rasteri/TAStm32/Src/usbplayback/gfx.c

#include <stdint.h>

const uint8_t GFX_CENTER[] = {
	0x00,0x00,
	0x00,0x00,
	0x00,0x00,
	0xc0,0x01,
	0x30,0x06,
	0x08,0x08,
	0x04,0x10,
	0x02,0x20,
	0x02,0x20,
	0x01,0x40,
	0x01,0x40,
	0x01,0x40,
	0x02,0x20,
	0x02,0x20,
	0x04,0x10,
	0x08,0x08,
	0x30,0x06,
	0xc0,0x01,
	0x00,0x00,
	0x00,0x00,
	0x00,0x00
};

const uint8_t GFX_START_ON[] = {
	//starton
	0x00,0xf0,0x03,
	0x00,0xfc,0x0f,
	0x00,0xfe,0x1f,
	0x00,0xc7,0x3b,
	0x00,0x83,0x33,
	0x80,0x1b,0x77,
	0x80,0x3b,0x77,
	0x80,0x3b,0x76,
	0x80,0x73,0x70,
	0x80,0xf7,0x78,
	0x80,0xff,0x7f,
	0x80,0xdf,0x7f,
	0x80,0x0f,0x78,
	0x80,0x07,0x70,
	0x80,0xdf,0x77,
	0x80,0xff,0x7f,
	0x80,0xbf,0x79,
	0x80,0xdf,0x70,
	0x80,0x5f,0x76,
	0x80,0x5f,0x77,
	0x80,0x1f,0x70,
	0x80,0x3f,0x70,
	0x80,0xff,0x7f,
	0x80,0xff,0x7f,
	0x80,0x1f,0x70,
	0x80,0x1f,0x70,
	0x80,0xdf,0x7f,
	0x80,0xdf,0x7f,
	0x80,0xdf,0x7f,
	0x80,0x0f,0x78,
	0x80,0x07,0x70,
	0x00,0xdf,0x37,
	0x00,0xff,0x3f,
	0x00,0xfe,0x1f,
	0x00,0xfc,0x0f,
	0x00,0xf0,0x03
};

const uint8_t GFX_SELECT_ON[] = {
	//selecton
	0xc0,0x0f,0x00,
	0x10,0x37,0x00,
	0x08,0x66,0x00,
	0x6c,0xee,0x00,
	0x6c,0xec,0x00,
	0xee,0xec,0x01,
	0xce,0xe0,0x01,
	0xde,0xf1,0x01,
	0xfe,0xff,0x01,
	0x7e,0xf0,0x01,
	0x3e,0xe0,0x01,
	0xbe,0xed,0x01,
	0xbe,0xed,0x01,
	0x3e,0xe4,0x01,
	0x7e,0xf4,0x01,
	0x0e,0xe0,0x01,
	0x0e,0xe0,0x01,
	0xfe,0xff,0x01,
	0x7e,0xf0,0x01,
	0x3e,0xe0,0x01,
	0xbe,0xed,0x01,
	0xbe,0xed,0x01,
	0x3e,0xe4,0x01,
	0x7e,0xf4,0x01,
	0x7e,0xf0,0x01,
	0x3e,0xe0,0x01,
	0xbe,0xef,0x01,
	0xbe,0xef,0x01,
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
		0xff,0x07,0x00,0x00,
		0xff,0x03,0x00,0x00,
		0xff,0x01,0x00,0x00,
		0xff,0x00,0x00,0x00,
		0x7f,0x00,0x00,0x00,
		0x3f,0x00,0x00,0x00,
		0x1f,0x00,0x00,0x00,
		0x0f,0x00,0x00,0x00,
		0x07,0x00,0x00,0x00,
		0x03,0x00,0x00,0x00,
		0x01,0x00,0x00,0x00,
		0x00,0x00,0x00,0x00
};
