rasteri/TAStm32/python/tastm32-dfu.py

#!/usr/bin/env python3
import serial, time
import serial_helper
import argparse_helper
import tastm32

parser = argparse_helper.audio_parser()
args = parser.parse_args()

tastm32.DEBUG = args.debug

if args.serial == None:
    dev = tastm32.TAStm32(serial_helper.select_serial_port())
else:
    dev = tastm32.TAStm32(args.serial)

# connect to device
ser = dev

print("--- Sending command to jump to DFU mode")

ser.write(b'\xDF')
time.sleep(0.1)
